NotARoomba/AI-Jukebox/pcb/Jukbox.kicad_pcb

## KiCad design schematics/backplane/backplane/bus connectos.kicad_sch

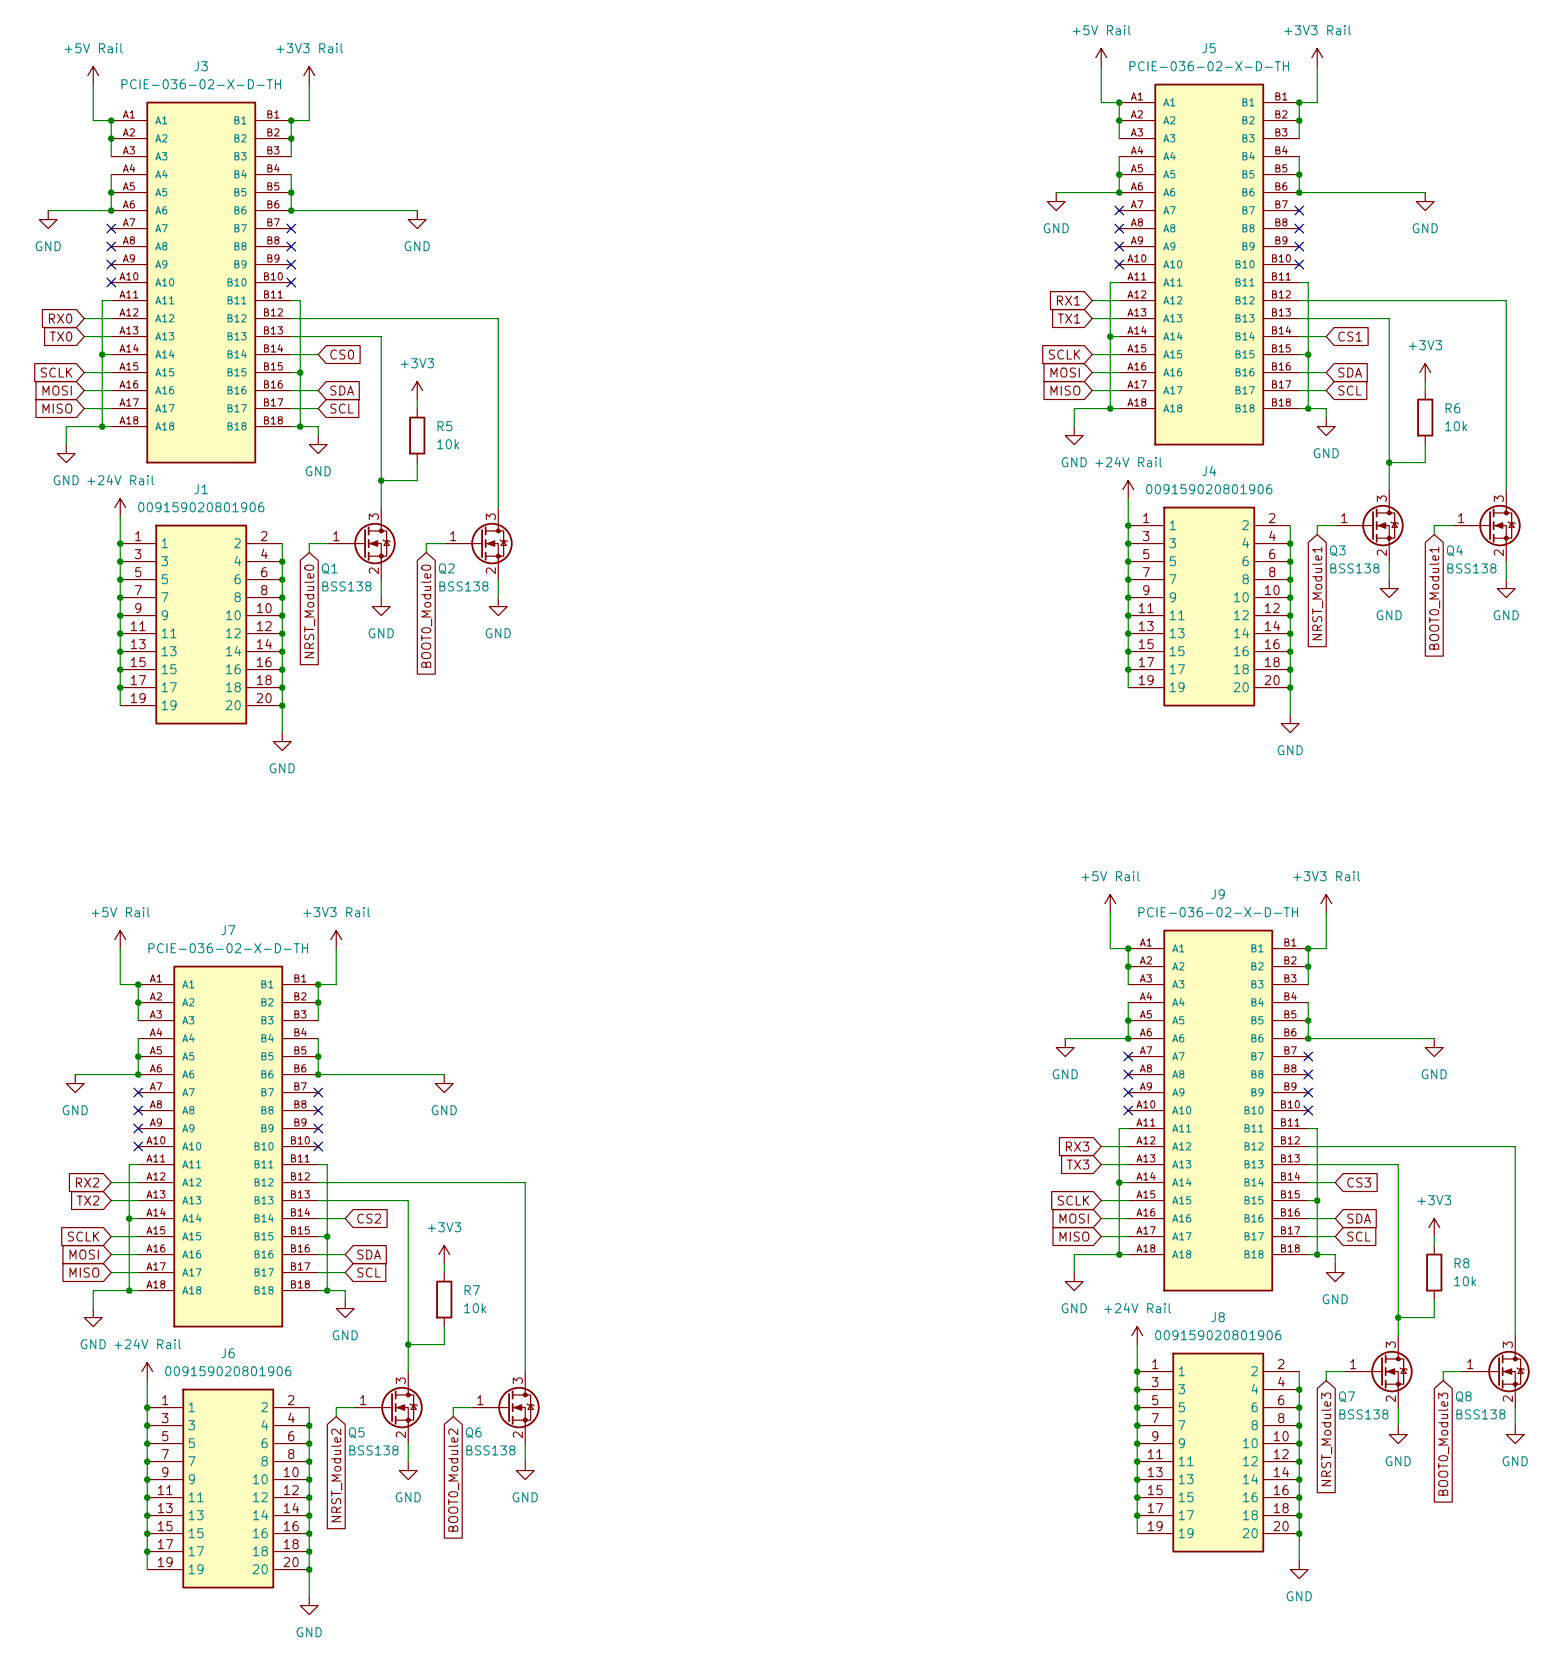
[picture p19: schematic bus connectos.kicad_sch]

Parts:
J1, J4, J6, J8: 009159020801906; Manufacturer_Part_Number 009159020801906
J3, J5, J7, J9: PCIE-036-02-X-D-TH; SAMTEC_PCIE-036-02-X-D-TH; PARTREV D
Q1, Q2, Q3, Q4, Q5, Q6, Q7, Q8: BSS138; SOT-23
R5, R6, R7, R8: 10k; R_0603_1608Metric

Connections:
+3V3: R5.1, R6.1, R7.1, R8.1
+3V3 Rail: J3.B1, J3.B2, J3.B3, J5.B1, J5.B2, J5.B3, J7.B1, J7.B2, J7.B3, J9.B1, J9.B2, J9.B3
+5V Rail: J3.A1, J3.A2, J3.A3, J5.A1, J5.A2, J5.A3, J7.A1, J7.A2, J7.A3, J9.A1, J9.A2, J9.A3
+24V Rail: J1.1, J1.3, J1.5, J1.7, J1.9, J1.11, J1.13, J1.15, J1.17, J1.19, J4.1, J4.3, J4.5, J4.7, J4.9, J4.11, J4.13, J4.15, J4.17, J4.19, J6.1, J6.3, J6.5, J6.7, J6.9, J6.11, J6.13, J6.15, J6.17, J6.19, J8.1, J8.3, J8.5, J8.7, J8.9, J8.11, J8.13, J8.15, J8.17, J8.19
BOOT0_Module0: Q2.1 (G)
BOOT0_Module1: Q4.1 (G)
BOOT0_Module2: Q6.1 (G)
BOOT0_Module3: Q8.1 (G)
CS0: J3.B14
CS1: J5.B14
CS2: J7.B14
CS3: J9.B14
GND: J1.2, J1.4, J1.6, J1.8, J1.10, J1.12, J1.14, J1.16, J1.18, J1.20, J3.A4, J3.A5, J3.A6, J3.A11, J3.A14, J3.A18, J3.B4, J3.B5, J3.B6, J3.B11, J3.B15, J3.B18, J4.2, J4.4, J4.6, J4.8, J4.10, J4.12, J4.14, J4.16, J4.18, J4.20, J5.A4, J5.A5, J5.A6, J5.A11, J5.A14, J5.A18, J5.B4, J5.B5, J5.B6, J5.B11, J5.B15, J5.B18, J6.2, J6.4, J6.6, J6.8, J6.10, J6.12, J6.14, J6.16, J6.18, J6.20, J7.A4, J7.A5, J7.A6, J7.A11, J7.A14, J7.A18, J7.B4, J7.B5, J7.B6, J7.B11, J7.B15, J7.B18, J8.2, J8.4, J8.6, J8.8, J8.10, J8.12, J8.14, J8.16, J8.18, J8.20, J9.A4, J9.A5, J9.A6, J9.A11, J9.A14, J9.A18, J9.B4, J9.B5, J9.B6, J9.B11, J9.B15, J9.B18, Q1.2 (S), Q2.2 (S), Q3.2 (S), Q4.2 (S), Q5.2 (S), Q6.2 (S), Q7.2 (S), Q8.2 (S)
MISO: J3.A17, J5.A17, J7.A17, J9.A17
MOSI: J3.A16, J5.A16, J7.A16, J9.A16
NRST_Module0: Q1.1 (G)
NRST_Module1: Q3.1 (G)
NRST_Module2: Q5.1 (G)
NRST_Module3: Q7.1 (G)
unnamed: J3.B12, Q2.3 (D)
unnamed: J3.B13, Q1.3 (D), R5.2
unnamed: J5.B12, Q4.3 (D)
unnamed: J5.B13, Q3.3 (D), R6.2
unnamed: J7.B12, Q6.3 (D)
unnamed: J7.B13, Q5.3 (D), R7.2
unnamed: J9.B12, Q8.3 (D)
unnamed: J9.B13, Q7.3 (D), R8.2
RX0: J3.A12
RX1: J5.A12
RX2: J7.A12
RX3: J9.A12
SCL: J3.B17, J5.B17, J7.B17, J9.B17
SCLK: J3.A15, J5.A15, J7.A15, J9.A15
SDA: J3.B16, J5.B16, J7.B16, J9.B16
TX0: J3.A13
TX1: J5.A13
TX2: J7.A13
TX3: J9.A13
