NotARoomba/AI-Jukebox/pcb/Jukbox.kicad_pcb

## KiCad design schematics/backplane/backplane/power_supply.kicad_sch

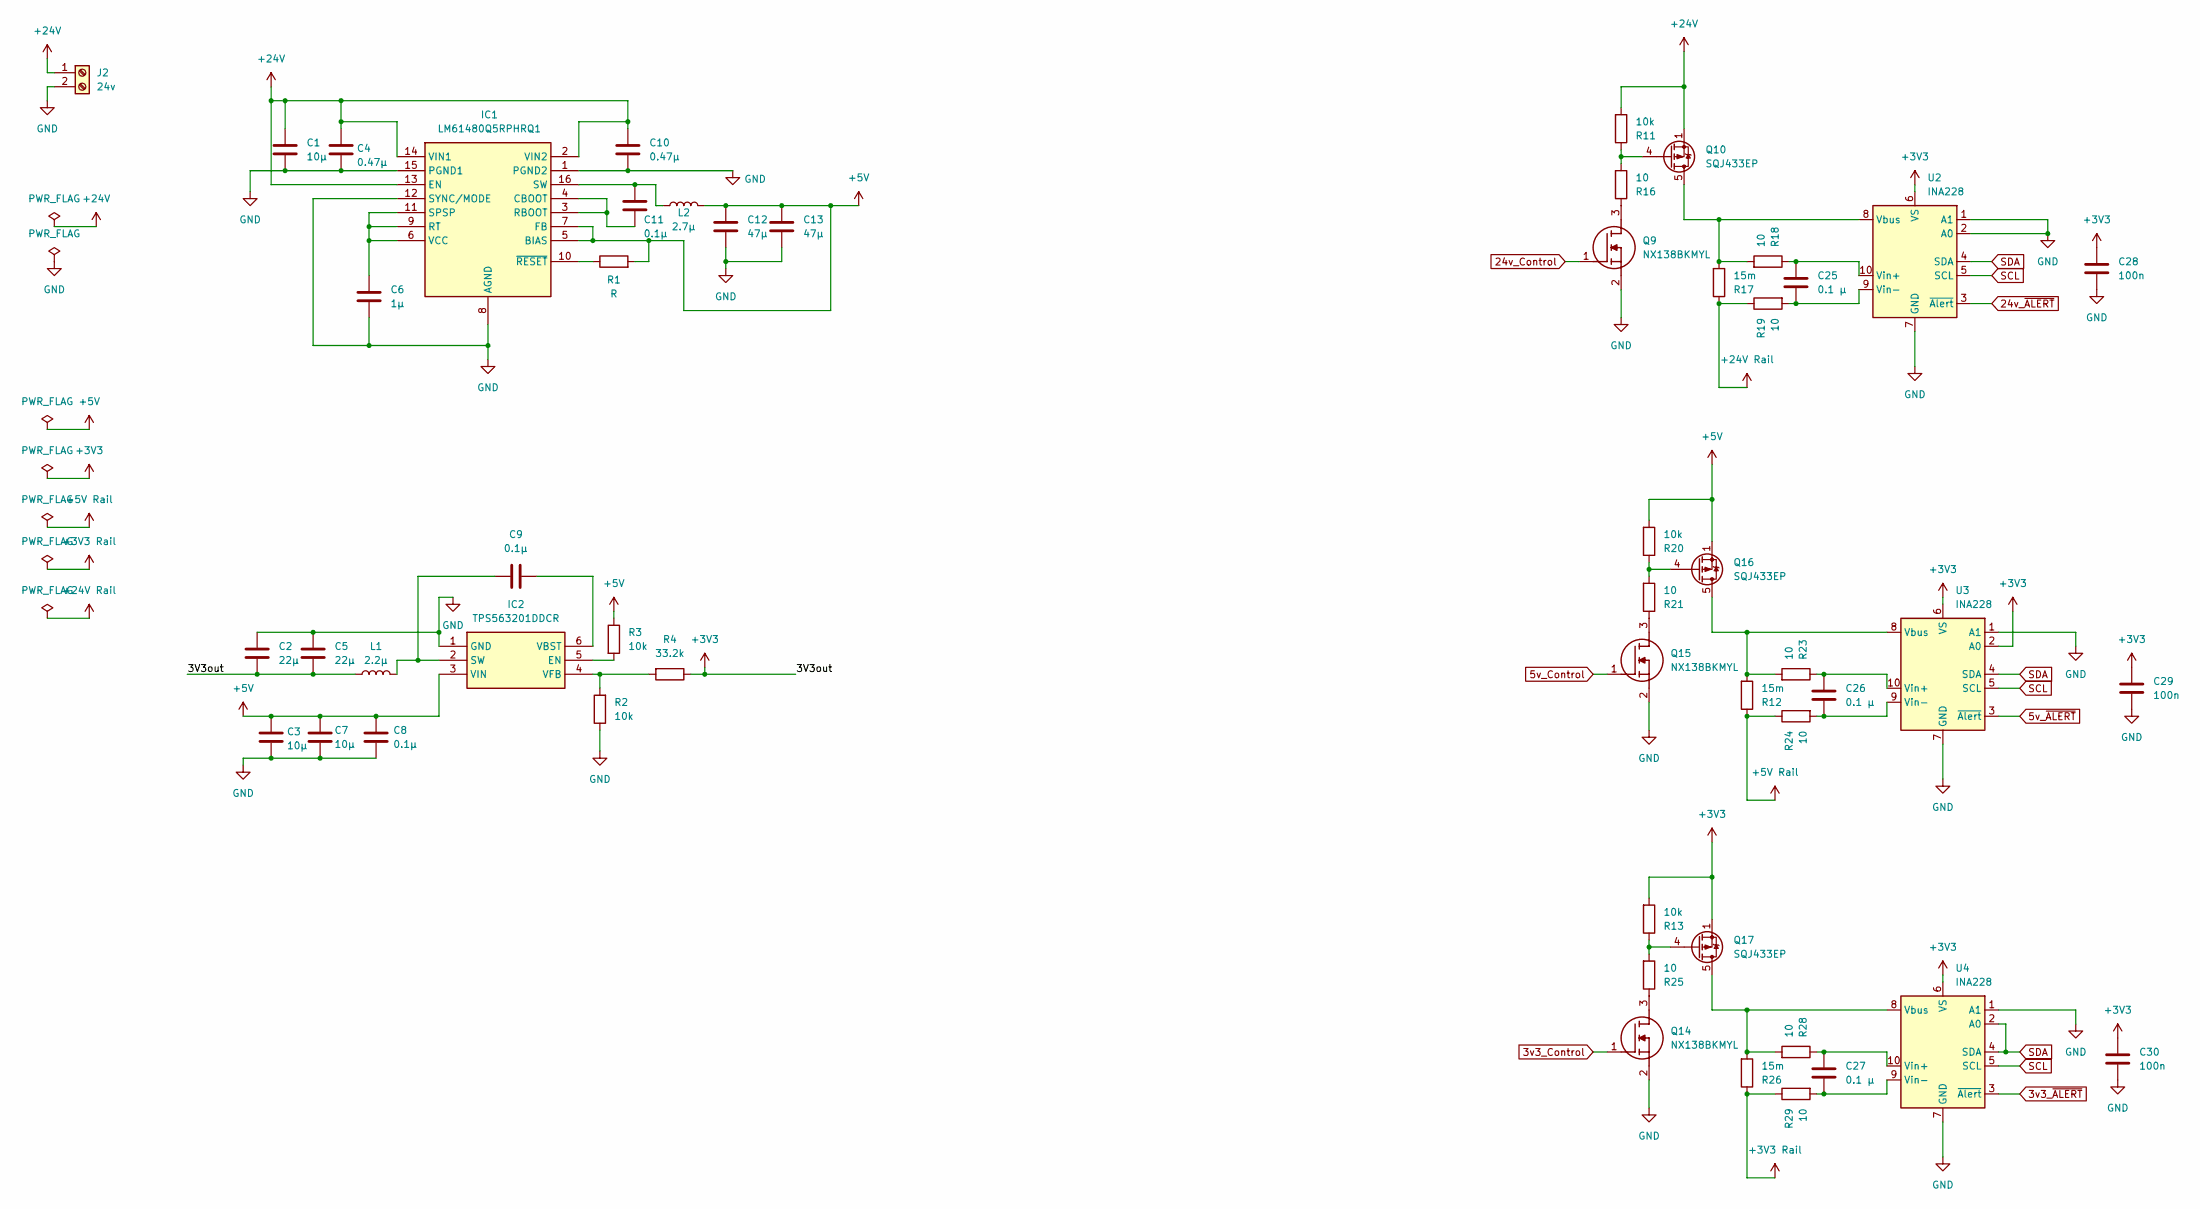
[picture p21: schematic power_supply.kicad_sch]

Parts:
C1, C3, C7: 10µ; C_0603_1608Metric
C2, C5: 22µ; C_0603_1608Metric
C4, C10: 0.47µ; C_0603_1608Metric
C6: 1µ; C_0603_1608Metric
C8, C9, C11: 0.1µ; C_0603_1608Metric
C12, C13: 47µ; C_0603_1608Metric
C25, C26, C27: 0.1 μ; C_0603_1608Metric
C28, C29, C30: 100n; C_0603_1608Metric
IC1: LM61480Q5RPHRQ1; LM61480Q4RPHRQ1; Mouser Part Number 595-LM61480Q5RPHRQ1
IC2: TPS563201DDCR; SOT95P280X110-6N; Mouser Part Number 595-TPS563201DDCR
J2: 24v; TerminalBlock_Wuerth_691311400102_P7.62mm
L1: 2.2µ
L2: 2.7µ; INDPM140128X650N
Q9, Q14, Q15: NX138BKMYL; Mouser Part Number 771-NX138BKMYL
Q10, Q16, Q17: SQJ433EP; PowerPAK_SO-8L_Single
R1: R; R_0603_1608Metric
R2, R3, R11, R13, R20: 10k; R_0603_1608Metric
R4: 33.2k; R_0603_1608Metric
R12, R17, R26: 15m; R_0603_1608Metric
R16, R18, R19, R21, R23, R24, R25, R28, R29: 10; R_0603_1608Metric
U2, U3, U4: INA228; VSSOP-10_3x3mm_P0.5mm

Connections:
3v3_Control: Q14.1 (G)
3v3_~ALERT: U4.3 (~Alert)
5v_Control: Q15.1 (G)
5v_~ALERT: U3.3 (~Alert)
24v_Control: Q9.1 (G)
24v_~ALERT: U2.3 (~Alert)
+3V3: C2.2, C5.2, C28.1, C29.1, C30.1, L1.1, Q17.1 (S), Q17.2 (S), Q17.3 (S), R4.1, R13.2, U2.6 (VS), U3.2 (A0), U3.6 (VS), U4.6 (VS)
+3V3 Rail: R26.1, R29.1
+5V: C3.1, C7.1, C8.1, C12.1, C13.1, IC1.5 (BIAS), IC1.7 (FB), IC2.3 (VIN), L2.2, Q16.1 (S), Q16.2 (S), Q16.3 (S), R1.2, R3.1, R20.2
+5V Rail: R12.1, R24.1
+24V: C1.1, C4.1, C10.1, IC1.2 (VIN2), IC1.13 (EN), IC1.14 (VIN1), J2.1, Q10.1 (S), Q10.2 (S), Q10.3 (S), R11.2
+24V Rail: R17.1, R19.1
GND: C1.2, C2.1, C3.2, C4.2, C5.1, C6.2, C7.2, C8.2, C10.2, C12.2, C13.2, C28.2, C29.2, C30.2, IC1.1 (PGND2), IC1.8 (AGND), IC1.12 (SYNC/MODE), IC1.15 (PGND1), IC2.1 (GND), J2.2, Q9.2 (S), Q14.2 (S), Q15.2 (S), R2.1, U2.1 (A1), U2.2 (A0), U2.7 (GND), U3.1 (A1), U3.7 (GND), U4.1 (A1), U4.7 (GND)
unnamed: C6.1, IC1.6 (VCC), IC1.9 (RT), IC1.11 (SPSP)
unnamed: C9.1, IC2.2 (SW), L1.2
unnamed: C9.2, IC2.6 (VBST)
unnamed: C11.1, IC1.16 (SW), L2.1
unnamed: C11.2, IC1.3 (RBOOT), IC1.4 (CBOOT)
unnamed: C25.1, R18.1, U2.10 (Vin+)
unnamed: C25.2, R19.2, U2.9 (Vin-)
unnamed: C26.1, R23.1, U3.10 (Vin+)
unnamed: C26.2, R24.2, U3.9 (Vin-)
unnamed: C27.1, R28.1, U4.10 (Vin+)
unnamed: C27.2, R29.2, U4.9 (Vin-)
unnamed: IC1.10 (~RESET), R1.1
unnamed: IC2.4 (VFB), R2.2, R4.2
unnamed: IC2.5 (EN), R3.2
unnamed: Q9.3 (D), R16.1
unnamed: Q10.4 (G), R11.1, R16.2
unnamed: Q10.5 (D), R17.2, R18.2, U2.8 (Vbus)
unnamed: Q14.3 (D), R25.1
unnamed: Q15.3 (D), R21.1
unnamed: Q16.4 (G), R20.1, R21.2
unnamed: Q16.5 (D), R12.2, R23.2, U3.8 (Vbus)
unnamed: Q17.4 (G), R13.1, R25.2
unnamed: Q17.5 (D), R26.2, R28.2, U4.8 (Vbus)
SCL: U2.5 (SCL), U3.5 (SCL), U4.5 (SCL)
SDA: U2.4 (SDA), U3.4 (SDA), U4.2 (A0), U4.4 (SDA)
